Imploo/BigNomad/PCB/NomadKeyboard.kicad_sch

## KiCad design PCB/NomadKeyboard.kicad_sch (2025-03-08)

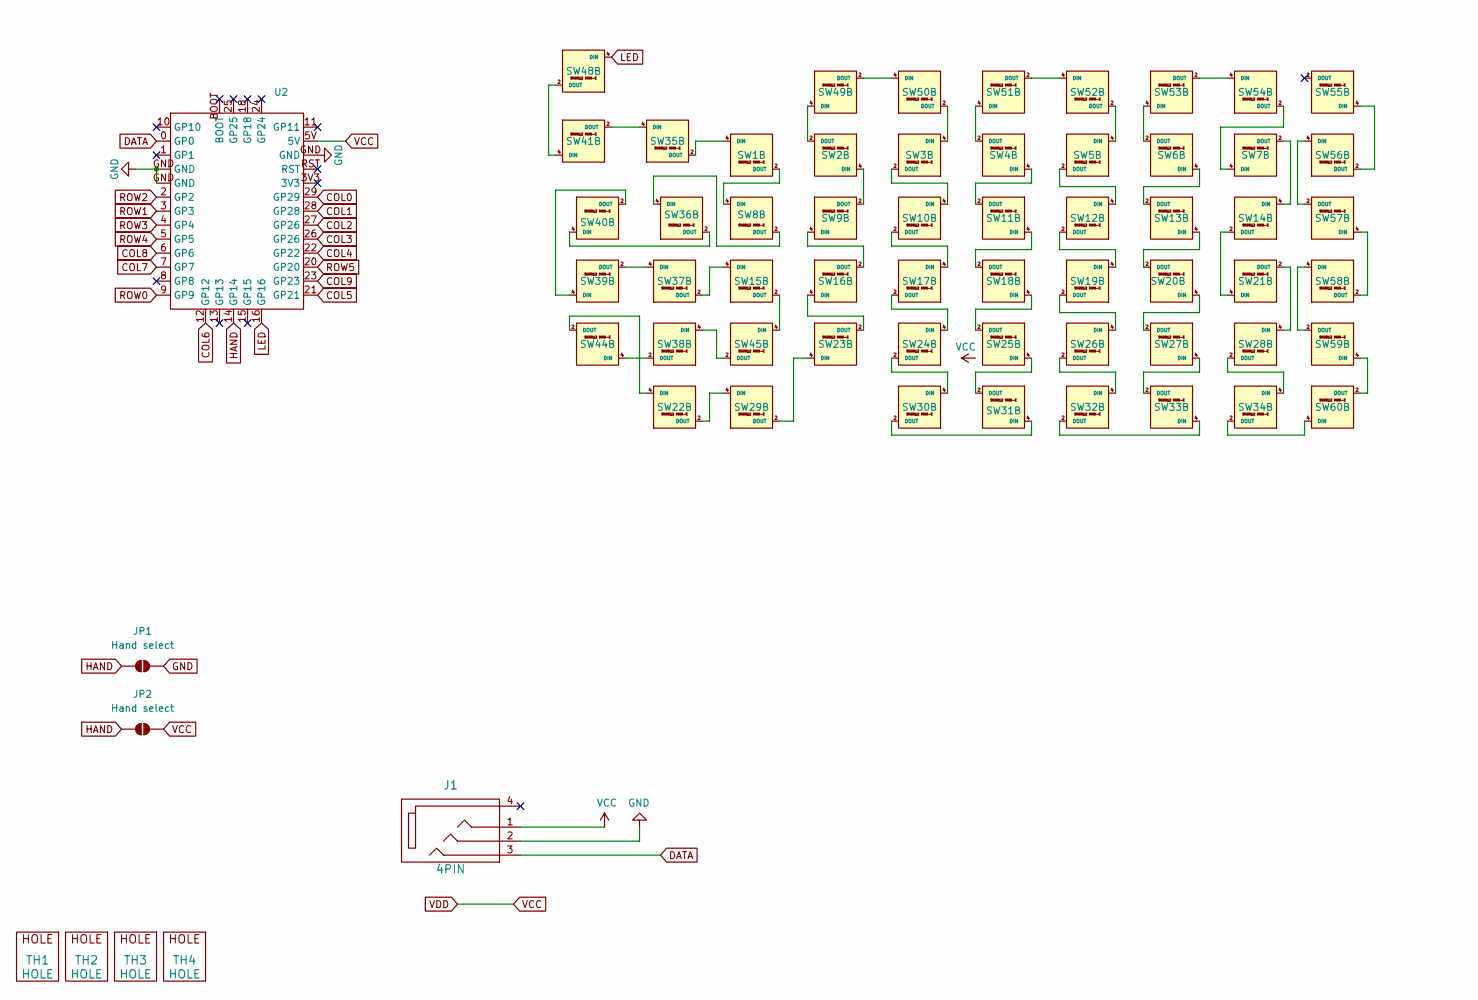
[picture p6: schematic NomadKeyboard.kicad_sch, part in row 1, column 1]

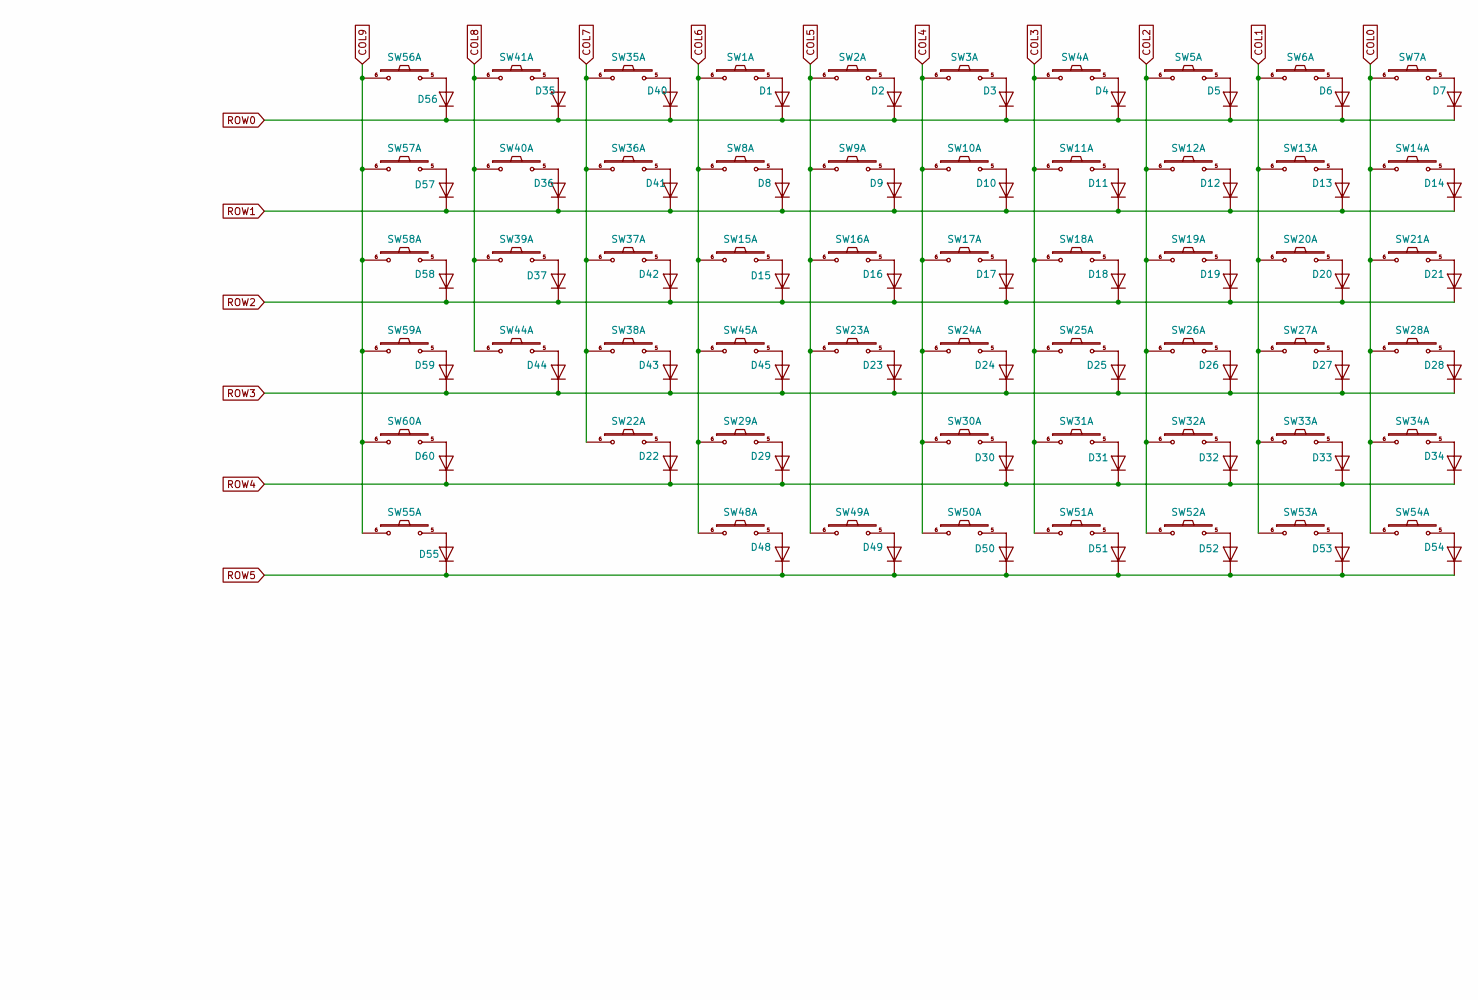
[picture p7: schematic NomadKeyboard.kicad_sch, part in row 1, column 2]

Parts:
D1, D2, D3, D4, D5, D6, D7, D8, D9, D10, D11, D12, D13, D14, D15, D16, D17, D18, D19, D20, D21, D22, D23, D24, D25, D26, D27, D28, D29, D30, D31, D32, D33, D34, D35, D36, D37, D40, D41, D42, D43, D44, D45, D48, D49, D50, D51, D52, D53, D54, D55, D56, D57, D58, D59, D60: D; crkbd-diode
J1: 4PIN; MJ-4PP-9
JP1, JP2: Hand select; SolderJumper-2_P1.3mm_Open_RoundedPad1.0x1.5mm
SW1, SW2, SW3, SW4, SW5, SW6, SW7, SW8, SW9, SW10, SW11, SW12, SW13, SW14, SW15, SW16, SW17, SW18, SW19, SW20, SW21, SW22, SW23, SW24, SW25, SW26, SW27, SW28, SW29, SW30, SW31, SW32, SW33, SW34, SW35, SW36, SW37, SW38, SW39, SW40, SW41, SW44, SW45, SW48, SW49, SW50, SW51, SW52, SW53, SW54, SW55, SW56, SW57, SW58, SW59, SW60: SW_PUSH_LED; Choc_Hotswap_SK6812MiniE
TH1, TH2, TH3, TH4: HOLE; HOLE_M2_TH
U2: pro_micro_rp2040

Connections:
COL0: SW7.6, SW14.6, SW21.6, SW28.6, SW34.6, SW54.6, U2.29 (GP29)
COL1: SW6.6, SW13.6, SW20.6, SW27.6, SW33.6, SW53.6, U2.28 (GP28)
COL2: SW5.6, SW12.6, SW19.6, SW26.6, SW32.6, SW52.6, U2.27 (GP26)
COL3: SW4.6, SW11.6, SW18.6, SW25.6, SW31.6, SW51.6, U2.26 (GP26)
COL4: SW3.6, SW10.6, SW17.6, SW24.6, SW30.6, SW50.6, U2.22 (GP22)
COL5: SW2.6, SW9.6, SW16.6, SW23.6, SW49.6, U2.21 (GP21)
COL6: SW1.6, SW8.6, SW15.6, SW29.6, SW45.6, SW48.6, U2.12 (GP12)
COL7: SW22.6, SW35.6, SW36.6, SW37.6, SW38.6, U2.7 (GP7)
COL8: SW39.6, SW40.6, SW41.6, SW44.6, U2.6 (GP6)
COL9: SW55.6, SW56.6, SW57.6, SW58.6, SW59.6, SW60.6, U2.23 (GP23)
DATA: J1.3, U2.0 (GP0)
GND: J1.2, JP1.2 (B), U2.GND
HAND: JP1.1 (A), JP2.1 (A), U2.14 (GP14)
LED: SW48.4 (DIN), U2.16 (GP16)
unnamed: D1.2 (A), SW1.5
unnamed: D2.2 (A), SW2.5
unnamed: D3.2 (A), SW3.5
unnamed: D4.2 (A), SW4.5
unnamed: D5.2 (A), SW5.5
unnamed: D6.2 (A), SW6.5
unnamed: D7.2 (A), SW7.5
unnamed: D8.2 (A), SW8.5
unnamed: D9.2 (A), SW9.5
unnamed: D10.2 (A), SW10.5
unnamed: D11.2 (A), SW11.5
unnamed: D12.2 (A), SW12.5
unnamed: D13.2 (A), SW13.5
unnamed: D14.2 (A), SW14.5
unnamed: D15.2 (A), SW15.5
unnamed: D16.2 (A), SW16.5
unnamed: D17.2 (A), SW17.5
unnamed: D18.2 (A), SW18.5
unnamed: D19.2 (A), SW19.5
unnamed: D20.2 (A), SW20.5
unnamed: D21.2 (A), SW21.5
unnamed: D22.2 (A), SW22.5
unnamed: D23.2 (A), SW23.5
unnamed: D24.2 (A), SW24.5
unnamed: D25.2 (A), SW25.5
unnamed: D26.2 (A), SW26.5
unnamed: D27.2 (A), SW27.5
unnamed: D28.2 (A), SW28.5
unnamed: D29.2 (A), SW29.5
unnamed: D30.2 (A), SW30.5
unnamed: D31.2 (A), SW31.5
unnamed: D32.2 (A), SW32.5
unnamed: D33.2 (A), SW33.5
unnamed: D34.2 (A), SW34.5
unnamed: D35.2 (A), SW41.5
unnamed: D36.2 (A), SW40.5
unnamed: D37.2 (A), SW39.5
unnamed: D40.2 (A), SW35.5
unnamed: D41.2 (A), SW36.5
unnamed: D42.2 (A), SW37.5
unnamed: D43.2 (A), SW38.5
unnamed: D44.2 (A), SW44.5
unnamed: D45.2 (A), SW45.5
unnamed: D48.2 (A), SW48.5
unnamed: D49.2 (A), SW49.5
unnamed: D50.2 (A), SW50.5
unnamed: D51.2 (A), SW51.5
unnamed: D52.2 (A), SW52.5
unnamed: D53.2 (A), SW53.5
unnamed: D54.2 (A), SW54.5
unnamed: D55.2 (A), SW55.5
unnamed: D56.2 (A), SW56.5
unnamed: D57.2 (A), SW57.5
unnamed: D58.2 (A), SW58.5
unnamed: D59.2 (A), SW59.5
unnamed: D60.2 (A), SW60.5
unnamed: SW1.2 (DOUT), SW8.4 (DIN)
unnamed: SW1.4 (DIN), SW35.2 (DOUT)
unnamed: SW2.2 (DOUT), SW49.4 (DIN)
unnamed: SW2.4 (DIN), SW9.2 (DOUT)
unnamed: SW3.4 (DIN), SW50.2 (DOUT)
unnamed: SW4.2 (DOUT), SW51.4 (DIN)
unnamed: SW5.4 (DIN), SW52.2 (DOUT)
unnamed: SW10.2 (DOUT), SW17.4 (DIN)
unnamed: SW3.2 (DOUT), SW10.4 (DIN)
unnamed: SW4.4 (DIN), SW11.2 (DOUT)
unnamed: SW11.4 (DIN), SW18.2 (DOUT)
unnamed: SW12.2 (DOUT), SW19.4 (DIN)
unnamed: SW5.2 (DOUT), SW12.4 (DIN)
unnamed: SW6.4 (DIN), SW13.2 (DOUT)
unnamed: SW13.4 (DIN), SW20.2 (DOUT)
unnamed: SW14.2 (DOUT), SW21.4 (DIN)
unnamed: SW7.2 (DOUT), SW14.4 (DIN)
unnamed: SW15.2 (DOUT), SW45.4 (DIN)
unnamed: SW15.4 (DIN), SW37.2 (DOUT)
unnamed: SW9.4 (DIN), SW16.2 (DOUT)
unnamed: SW16.4 (DIN), SW23.2 (DOUT)
unnamed: SW17.2 (DOUT), SW24.4 (DIN)
unnamed: SW18.4 (DIN), SW25.2 (DOUT)
unnamed: SW19.2 (DOUT), SW26.4 (DIN)
unnamed: SW20.4 (DIN), SW27.2 (DOUT)
unnamed: SW21.2 (DOUT), SW28.4 (DIN)
unnamed: SW22.2 (DOUT), SW29.4 (DIN)
unnamed: SW22.4 (DIN), SW44.2 (DOUT)
unnamed: SW23.4 (DIN), SW29.2 (DOUT)
unnamed: SW24.2 (DOUT), SW30.4 (DIN)
unnamed: SW25.4 (DIN), SW31.2 (DOUT)
unnamed: SW26.2 (DOUT), SW32.4 (DIN)
unnamed: SW27.4 (DIN), SW33.2 (DOUT)
unnamed: SW28.2 (DOUT), SW34.4 (DIN)
unnamed: SW30.2 (DOUT), SW31.4 (DIN)
unnamed: SW32.2 (DOUT), SW33.4 (DIN)
unnamed: SW34.2 (DOUT), SW60.4 (DIN)
unnamed: SW35.4 (DIN), SW41.2 (DOUT)
unnamed: SW36.2 (DOUT), SW40.4 (DIN)
unnamed: SW8.2 (DOUT), SW36.4 (DIN)
unnamed: SW37.4 (DIN), SW39.2 (DOUT)
unnamed: SW38.2 (DOUT), SW44.4 (DIN)
unnamed: SW38.4 (DIN), SW45.2 (DOUT)
unnamed: SW39.4 (DIN), SW40.2 (DOUT)
unnamed: SW41.4 (DIN), SW48.2 (DOUT)
unnamed: SW49.2 (DOUT), SW50.4 (DIN)
unnamed: SW51.2 (DOUT), SW52.4 (DIN)
unnamed: SW53.2 (DOUT), SW54.4 (DIN)
unnamed: SW6.2 (DOUT), SW53.4 (DIN)
unnamed: SW7.4 (DIN), SW54.2 (DOUT)
unnamed: SW55.4 (DIN), SW56.2 (DOUT)
unnamed: SW56.4 (DIN), SW57.2 (DOUT)
unnamed: SW57.4 (DIN), SW58.2 (DOUT)
unnamed: SW58.4 (DIN), SW59.2 (DOUT)
unnamed: SW59.4 (DIN), SW60.2 (DOUT)
ROW0: D1.1 (K), D2.1 (K), D3.1 (K), D4.1 (K), D5.1 (K), D6.1 (K), D7.1 (K), D35.1 (K), D40.1 (K), D56.1 (K), U2.9 (GP9)
ROW1: D8.1 (K), D9.1 (K), D10.1 (K), D11.1 (K), D12.1 (K), D13.1 (K), D14.1 (K), D36.1 (K), D41.1 (K), D57.1 (K), U2.3 (GP3)
ROW2: D15.1 (K), D16.1 (K), D17.1 (K), D18.1 (K), D19.1 (K), D20.1 (K), D21.1 (K), D37.1 (K), D42.1 (K), D58.1 (K), U2.2 (GP2)
ROW3: D23.1 (K), D24.1 (K), D25.1 (K), D26.1 (K), D27.1 (K), D28.1 (K), D43.1 (K), D44.1 (K), D45.1 (K), D59.1 (K), U2.4 (GP4)
ROW4: D22.1 (K), D29.1 (K), D30.1 (K), D31.1 (K), D32.1 (K), D33.1 (K), D34.1 (K), D60.1 (K), U2.5 (GP5)
ROW5: D48.1 (K), D49.1 (K), D50.1 (K), D51.1 (K), D52.1 (K), D53.1 (K), D54.1 (K), D55.1 (K), U2.20 (GP20)
VCC: J1.1, JP2.2 (B), SW25.1 (VDD), U2.5V
